janfiess/energiepark/Holz/Dependencies/Headphone_Station/mc/00_Button/Demo.gif

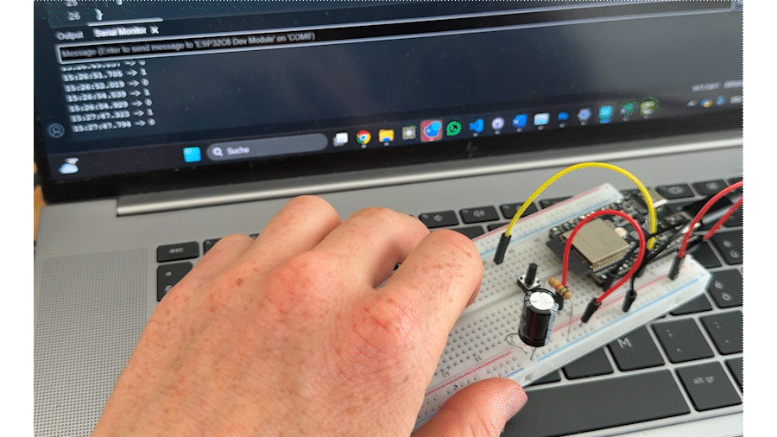
Holz/Dependencies/Headphone_Station/mc/00_Button/Demo.gif
