janfiess/energiepark/Dependencies/mc/audio1de/09_WLAN+MQTT+NFC+TOF+LED-Ring/Steckplan.png

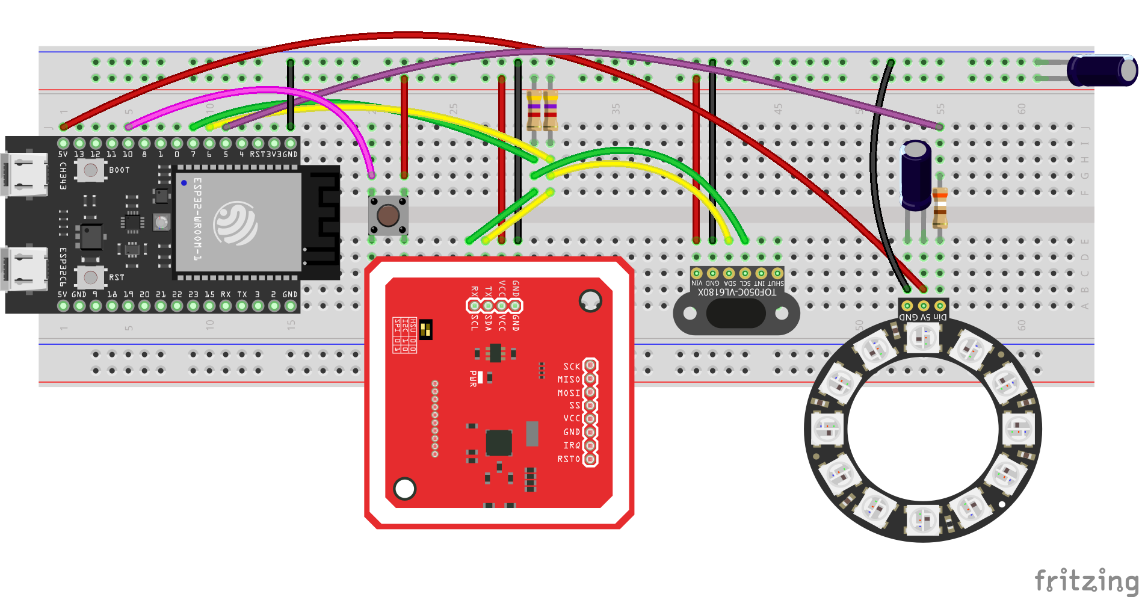
Dependencies/mc/audio1de/09_WLAN+MQTT+NFC+TOF+LED-Ring/Steckplan.png
