janfiess/energiepark/Holz/Assets/RFID-Scanner Watt steckt da drin/NEU_Startscreens_1.2 Startscreen.png

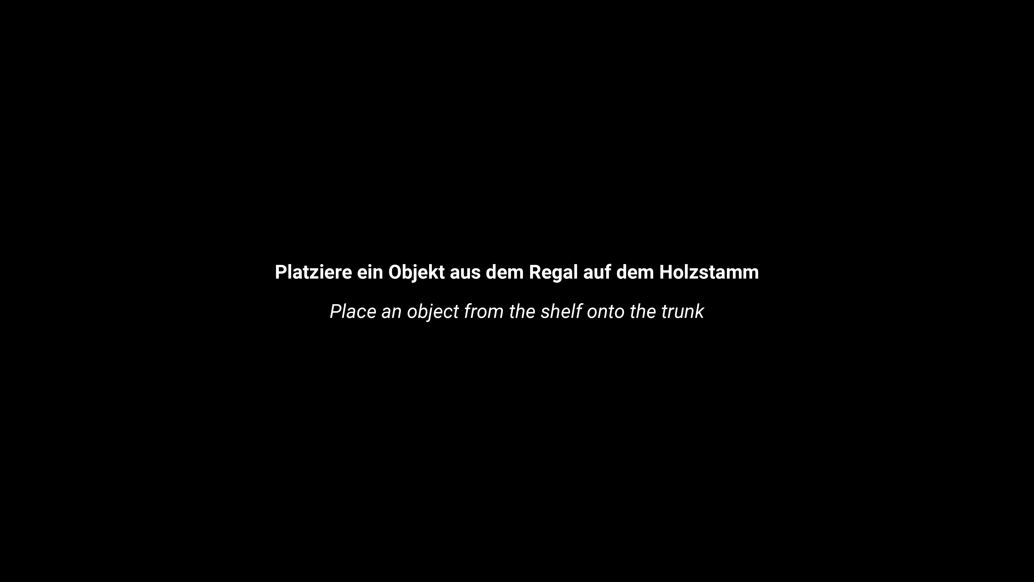
Holz/Assets/RFID-Scanner Watt steckt da drin/NEU_Startscreens_1.2 Startscreen.png
