janfiess/energiepark/Holz/Dependencies/Headphone_Station/mc/00_Button/Steckplan_mit_Pulldown.png

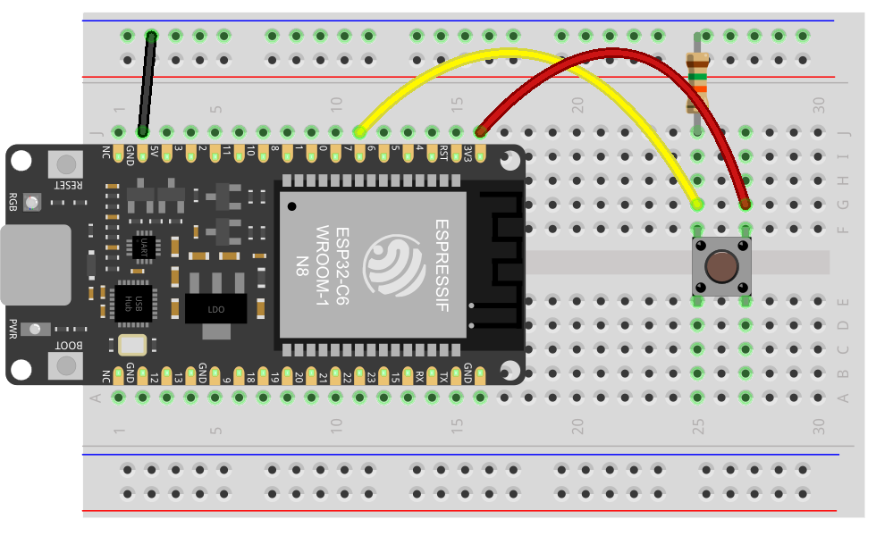
Holz/Dependencies/Headphone_Station/mc/00_Button/Steckplan_mit_Pulldown.png
