janfiess/energiepark/Holz/Dependencies/Headphone_Station/mc/Steckplan.png

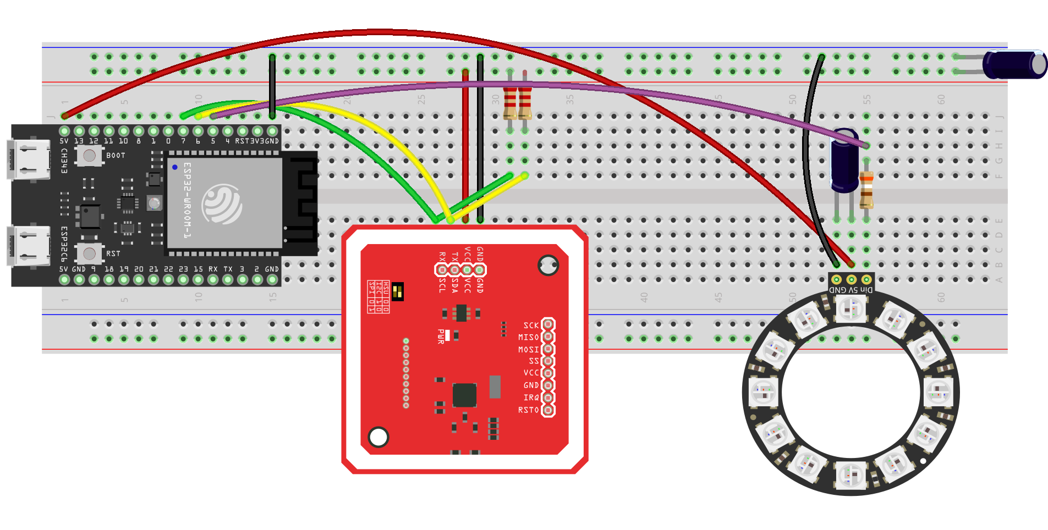
Holz/Dependencies/Headphone_Station/mc/Steckplan.png
