janfiess/energiepark/Sonne/Assets/Background.jpg

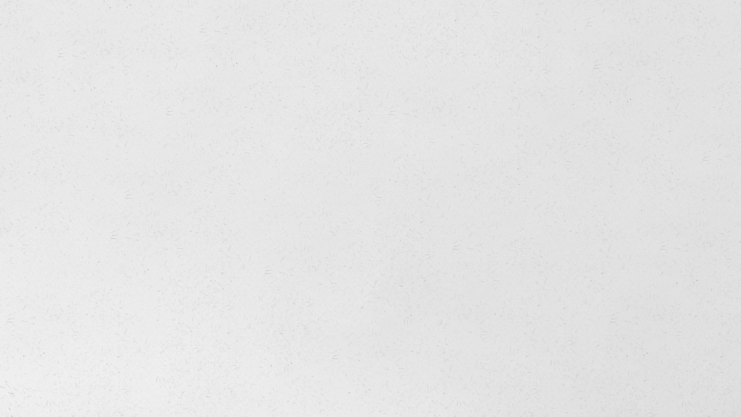
Sonne/Assets/Background.jpg
