janfiess/energiepark/Sonne/Dependencies/mc/Steckplan.png

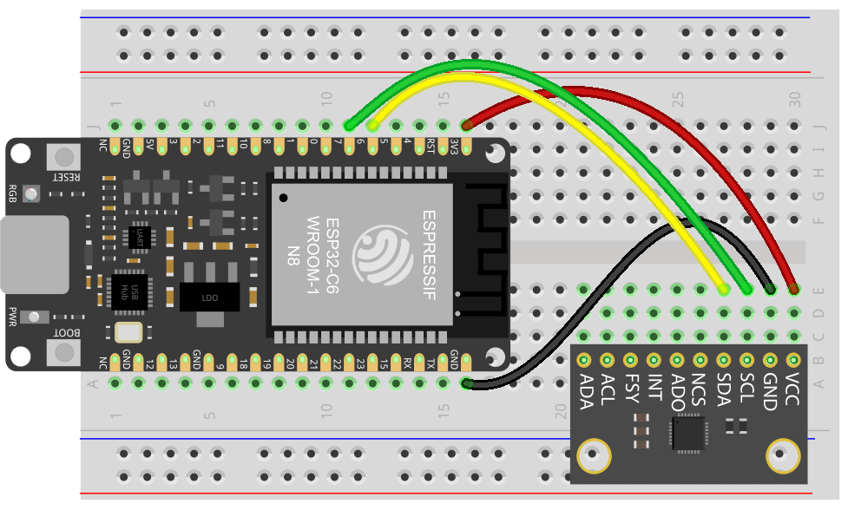
Sonne/Dependencies/mc/Steckplan.png
