janfiess/energiepark/Holz/Dependencies/Headphone_Station/mc/02_TOF_Test/Steckplan.png

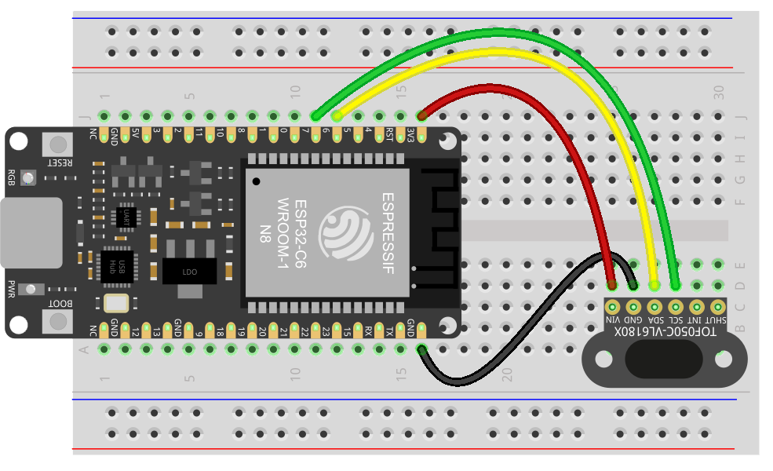
Holz/Dependencies/Headphone_Station/mc/02_TOF_Test/Steckplan.png
