janfiess/energiepark/Holz/Dependencies/Headphone_Station/mc/03_LED-Ring_test/Steckplan.png

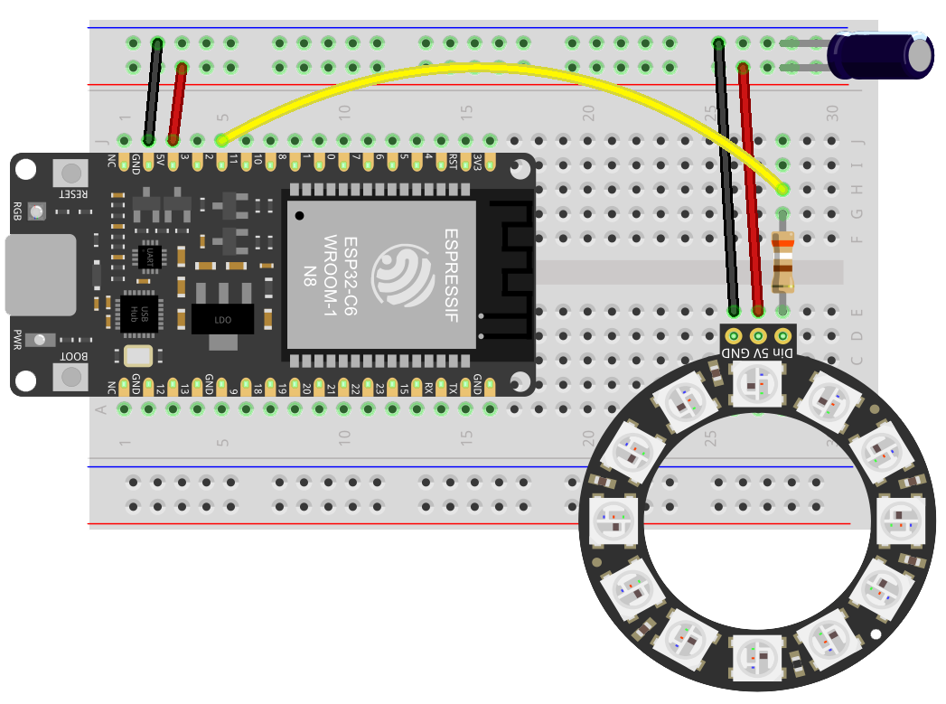
Holz/Dependencies/Headphone_Station/mc/03_LED-Ring_test/Steckplan.png
