janfiess/energiepark/Sonne/Dependencies/mc/01_Lagesensor_UART/01_Lagesensor_UART.ino

/**********************************************************************************************
*  ICM20948.ino
*  ICM20948 9-Degrees-of-Freedom
*  basiert auf example code: ICM20948_06_angles_and_orientation.ino
*  Messe Neigung, Beschleunigung usw. (Beschleunigungssensor + Gyroskop + Magnetometer)
*  Installiere ICM20948_WE Library von Wolfgang Ewald.
*  4 Anschlüsse an ESP32-C6 (Kommunikation per I2C -> dafür braucht es die vorinstallierte Wire-Library):
*  Sensor: Vin  <->  ESP32-C6: 3.3V 
*  Sensor: GND  <->  ESP32-C6: GND
*  Sensor: SDA  <->  ESP32-C6: GPIO6
*  Sensor: SCL  <->  ESP32-C6: GPIO7
***********************************************************************************************/


#include <Wire.h>
#include <ICM20948_WE.h>
#define ICM20948_ADDR 0x68

/* There are several ways to create your ICM20948 object:
 * ICM20948_WE myIMU = ICM20948_WE()              -> uses Wire / I2C Address = 0x68
 * ICM20948_WE myIMU = ICM20948_WE(ICM20948_ADDR) -> uses Wire / ICM20948_ADDR
 * ICM20948_WE myIMU = ICM20948_WE(&wire2)        -> uses the TwoWire object wire2 / ICM20948_ADDR
 * ICM20948_WE myIMU = ICM20948_WE(&wire2, ICM20948_ADDR) -> all together
 * ICM20948_WE myIMU = ICM20948_WE(CS_PIN, spi);  -> uses SPI, spi is just a flag, see SPI example
 * ICM20948_WE myIMU = ICM20948_WE(&SPI, CS_PIN, spi);  -> uses SPI / passes the SPI object, spi is just a flag, see SPI example
 */
ICM20948_WE myIMU = ICM20948_WE(ICM20948_ADDR);

void setup() {
  //delay(2000); // maybe needed for some MCUs, in particular for startup after power off
  Wire.begin(6,7);
  Serial.begin(115200);
  while(!Serial) {}
  
  if(!myIMU.init()){
    Serial.println("ICM20948 does not respond");
  }
  else{
    Serial.println("ICM20948 is connected");
  }

  /*  This is a method to calibrate. You have to determine the minimum and maximum 
   *  raw acceleration values of the axes determined in the range +/- 2 g. 
   *  You call the function as follows: setAccOffsets(xMin,xMax,yMin,yMax,zMin,zMax);
   *  The parameters are floats. 
   *  The calibration changes the slope / ratio of raw acceleration vs g. The zero point is 
   *  set as (min + max)/2.
   */
  //myIMU.setAccOffsets(-16330.0, 16450.0, -16600.0, 16180.0, -16520.0, 16690.0);
    
  /* The starting point, if you position the ICM20948 flat, is not necessarily 0g/0g/1g for x/y/z. 
   * The autoOffset function measures offset. It assumes your ICM20948 is positioned flat with its 
   * x,y-plane. The more you deviate from this, the less accurate will be your results.
   * It overwrites the zero points of setAccOffsets, but keeps the correction of the slope.
   * The function also measures the offset of the gyroscope data. The gyroscope offset does not   
   * depend on the positioning.
   * This function needs to be called after setAccOffsets but before other settings since 
   * it will overwrite settings!
   * You can query the offsets with the function:
   * xyzFloat getAccOffsets()
   * You can apply the offset using:
   * setAccOffsets(xyzFloat yourOffsets)
   */
  Serial.println("Position your ICM20948 flat and don't move it - calibrating...");
  delay(1000);
  myIMU.autoOffsets();
  Serial.println("Done!"); 
  
  /* enables or disables the acceleration sensor, default: enabled */
  // myIMU.enableAcc(true);

  /*  ICM20948_ACC_RANGE_2G      2 g   (default)
   *  ICM20948_ACC_RANGE_4G      4 g
   *  ICM20948_ACC_RANGE_8G      8 g   
   *  ICM20948_ACC_RANGE_16G    16 g
   */
  myIMU.setAccRange(ICM20948_ACC_RANGE_2G);
  
  /*  Choose a level for the Digital Low Pass Filter or switch it off.  
   *  ICM20948_DLPF_0, ICM20948_DLPF_2, ...... ICM20948_DLPF_7, ICM20948_DLPF_OFF 
   *  
   *  IMPORTANT: This needs to be ICM20948_DLPF_7 if DLPF is used in cycle mode!
   *  
   *  DLPF       3dB Bandwidth [Hz]      Output Rate [Hz]
   *    0              246.0               1125/(1+ASRD) 
   *    1              246.0               1125/(1+ASRD)
   *    2              111.4               1125/(1+ASRD)
   *    3               50.4               1125/(1+ASRD)
   *    4               23.9               1125/(1+ASRD)
   *    5               11.5               1125/(1+ASRD)
   *    6                5.7               1125/(1+ASRD) 
   *    7              473.0               1125/(1+ASRD)
   *    OFF           1209.0               4500
   *    
   *    ASRD = Accelerometer Sample Rate Divider (0...4095)
   *    You achieve lowest noise using level 6  
   */
  myIMU.setAccDLPF(ICM20948_DLPF_6);    
  
  /*  Acceleration sample rate divider divides the output rate of the accelerometer.
   *  Sample rate = Basic sample rate / (1 + divider) 
   *  It can only be applied if the corresponding DLPF is not off!
   *  Divider is a number 0...4095 (different range compared to gyroscope)
   *  If sample rates are set for the accelerometer and the gyroscope, the gyroscope
   *  sample rate has priority.
   */
  myIMU.setAccSampleRateDivider(10);
}

void loop() {
  xyzFloat gValue;
  xyzFloat angle;
  myIMU.readSensor();
  myIMU.getGValues(&gValue);
  myIMU.getAngles(&angle);
  
/* For g-values the corrected raws are used */
/*
  Serial.print("g-x      = ");
  Serial.print(gValue.x);
  Serial.print("  |  g-y      = ");
  Serial.print(gValue.y);
  Serial.print("  |  g-z      = ");
  Serial.println(gValue.z);
  */

/* Angles are also based on the corrected raws. Angles are simply calculated by
   angle = arcsin(g Value) */
  Serial.print("x:");
  Serial.print(angle.x);
  Serial.print(",y:");
  Serial.print(angle.y);
  Serial.print(",z:");
  Serial.println(angle.z);

  // Serial.print("Orientation of the module: ");
  //Serial.println(myIMU.getOrientationAsString());

  delay(300);
}
