janfiess/energiepark/Holz/Dependencies/Headphone_Station/mc/01_NFC_RFID_Test/i2c_scanner/i2c_scanner.ino

#include <Wire.h>

void setup() {
  Wire.begin(6,7); // Standard: SDA = GPIO21, SCL = GPIO22 (je nach Board ggf. anpassen)
  Serial.begin(115200);
  while (!Serial); // Warten bis Serial verfügbar ist
  Serial.println("\nI2C Scanner");
}

void loop() {
  byte error, address;
  int nDevices = 0;

  Serial.println("Scanning...");

  for (address = 1; address < 127; address++) {
    Wire.beginTransmission(address);
    error = Wire.endTransmission();

    if (error == 0) {
      Serial.print("I2C device found at address 0x");
      if (address < 16) Serial.print("0");
      Serial.print(address, HEX);
      Serial.println("  ✓");

      nDevices++;
    } else if (error == 4) {
      Serial.print("Unknown error at address 0x");
      if (address < 16) Serial.print("0");
      Serial.println(address, HEX);
    }
  }

  if (nDevices == 0)
    Serial.println("No I2C devices found\n");
  else
    Serial.println("Scan complete\n");

  delay(5000); // alle 5 Sekunden neu scannen
}
